mlab-modules/USBSERIALREADER01/doc/gen/dxf/USBSDREADER01-B_Courtyard.dxf

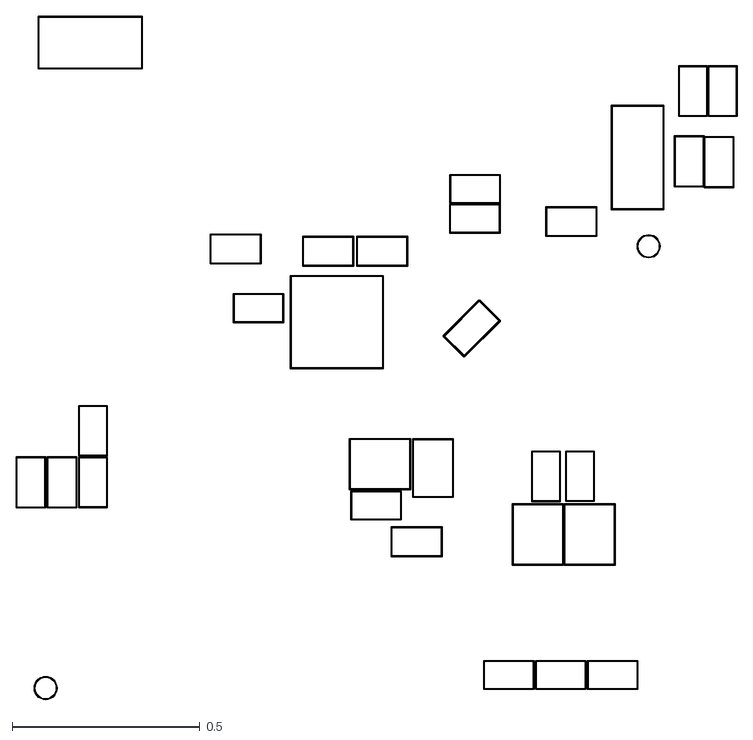
[picture p8: CAD file, 2023-09-27]
doc/gen/dxf/USBSDREADER01-B_Courtyard.dxf
1.92 x 1.82
