mlab-modules/USBSERIALREADER01/doc/gen/dxf/USBSDREADER01-B_Cu.dxf

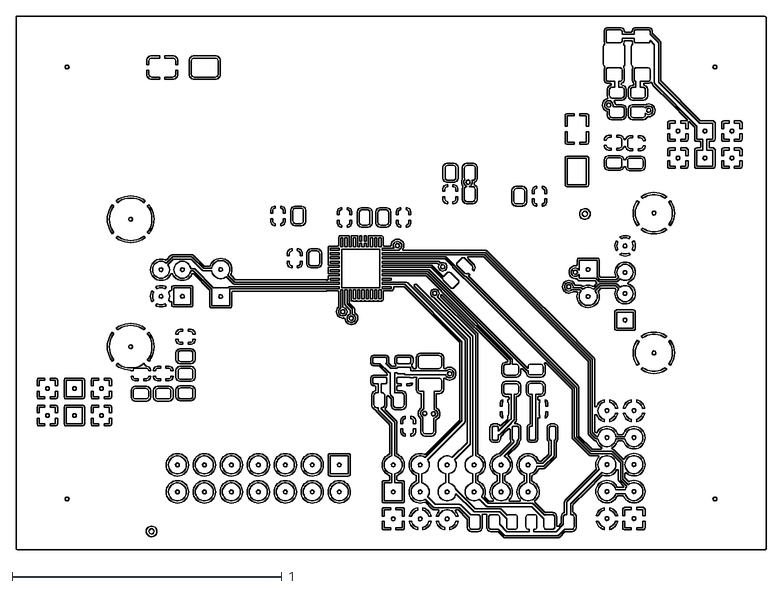
[picture p9: CAD file, 2023-09-27]
doc/gen/dxf/USBSDREADER01-B_Cu.dxf
2.78 x 1.98
